leogmendoza/chip8-emulator/platform/stm32/rom_catalog.c

#include "rom_catalog.h"

#ifdef PLATFORM_STM32

#include <stdint.h>

// -- ROM List --
const char *rom_list[] = {
    "tetris",
    "space_invaders",
    "tic_tac_toe",
    "brix",
    "pong",
    "connect_4",
    "puzzle",
    "blinky",
    "test_opcode"
};
const int rom_count = (int)(sizeof(rom_list) / sizeof(rom_list[0]));

// -- ROM configs --
// TODO: Change each ROM's config params when PCB arrives!!!
const RomConfig rom_configs[] = {
    { "tetris",         DEFAULT_INSTRUCTIONS_PER_FRAME, DEFAULT_CPU_CYCLE_DELAY_MS },
    { "space_invaders", DEFAULT_INSTRUCTIONS_PER_FRAME, DEFAULT_CPU_CYCLE_DELAY_MS },
    { "tic_tac_toe",    30, DEFAULT_CPU_CYCLE_DELAY_MS },
    { "brix",           15, DEFAULT_CPU_CYCLE_DELAY_MS },
    { "pong",           15, DEFAULT_CPU_CYCLE_DELAY_MS },
    { "connect_4",      10, DEFAULT_CPU_CYCLE_DELAY_MS },
    { "puzzle",         DEFAULT_INSTRUCTIONS_PER_FRAME, DEFAULT_CPU_CYCLE_DELAY_MS },
    { "blinky",         DEFAULT_INSTRUCTIONS_PER_FRAME, DEFAULT_CPU_CYCLE_DELAY_MS },
    { "test_opcode",    DEFAULT_INSTRUCTIONS_PER_FRAME, DEFAULT_CPU_CYCLE_DELAY_MS },
};
const int rom_config_count = sizeof(rom_configs) / sizeof(rom_configs[0]);

// -- ROM Hex Dumps -- 
const uint8_t rom_tetris[] = {
  0xa2, 0xb4, 0x23, 0xe6, 0x22, 0xb6, 0x70, 0x01, 0xd0, 0x11, 0x30, 0x25,
  0x12, 0x06, 0x71, 0xff, 0xd0, 0x11, 0x60, 0x1a, 0xd0, 0x11, 0x60, 0x25,
  0x31, 0x00, 0x12, 0x0e, 0xc4, 0x70, 0x44, 0x70, 0x12, 0x1c, 0xc3, 0x03,
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
  0x80, 0x80, 0x80, 0x80, 0x80, 0x80, 0x80, 0x80, 0x80, 0x80, 0x80, 0x80,
  0x1a, 0x1a, 0x1a, 0x1a, 0x1a, 0x1a, 0x1a, 0x1a, 0x1a, 0x1a, 0x1a, 0x1a,
  0x1a, 0x1a
};
const int rom_connect_4_len = sizeof(rom_connect_4);

#endif
