leogmendoza/chip8-emulator/platform/pc/display.c

#include "display.h"

#ifdef PLATFORM_PC

#include <SDL2/SDL.h>

#include "chip8.h"

typedef struct {
    SDL_Window   *window;
    SDL_Renderer *renderer;
    SDL_Texture  *texture;
} SdlVideoConfig;

static SdlVideoConfig sdl_video_config = {NULL, NULL, NULL};
static uint32_t pixels[DISPLAY_SIZE];

int platform_display_init(int scale) {
    // Set up SDL video subsystem
    if (SDL_Init(SDL_INIT_VIDEO) < 0) {
        SDL_Log("SDL video subsystem could not be initialized: %s\n", SDL_GetError());

        return 1;
    }

    // Create scaled-up window (currently from 64x32 to 640x320)
    sdl_video_config.window = SDL_CreateWindow(
        "CHIP-8 Emulator by Leopoldo Mendoza",
        SDL_WINDOWPOS_CENTERED, SDL_WINDOWPOS_CENTERED,
        DISPLAY_WIDTH * scale, DISPLAY_HEIGHT * scale,
        SDL_WINDOW_SHOWN
    );

    if (!sdl_video_config.window) {
        SDL_Log("Window could not be created: %s\n", SDL_GetError());

        return 1;
    }

    // Create accelerated renderer
    sdl_video_config.renderer = SDL_CreateRenderer(sdl_video_config.window, -1, SDL_RENDERER_ACCELERATED);

    if (!sdl_video_config.renderer) {
        SDL_Log("Renderer could not be created: %s\n", SDL_GetError());

        return 1;
    }

    // Create texture (64x32 pixel buffer, 32-bit RGBA format)
    sdl_video_config.texture = SDL_CreateTexture(
        sdl_video_config.renderer,
        SDL_PIXELFORMAT_RGBA8888,
        SDL_TEXTUREACCESS_STREAMING,
        DISPLAY_WIDTH,
        DISPLAY_HEIGHT
    );
    if (!sdl_video_config.texture) {
        SDL_Log("Texture could not be created: %s\n", SDL_GetError());
         
        return 1;
    }

    return 0;
}

void platform_display_destroy(void) {
    SDL_DestroyTexture(sdl_video_config.texture);
    SDL_DestroyRenderer(sdl_video_config.renderer);
    SDL_DestroyWindow(sdl_video_config.window);
    SDL_Quit();
}

void platform_display_draw(const uint8_t *framebuffer) {
    // Map CHIP-8 display to 32-bit white or black
    for (int i = 0; i < DISPLAY_SIZE; i++) {
        pixels[i] = ( framebuffer[i] ? 0xFFFFFFFF : 0x000000FF );
    }

    // Copy pixels into texture
    SDL_UpdateTexture(sdl_video_config.texture, NULL, pixels, DISPLAY_WIDTH * sizeof(uint32_t));

    // Clear window
    SDL_RenderClear(sdl_video_config.renderer);

    // Copy texture onto window
    SDL_RenderCopy(sdl_video_config.renderer, sdl_video_config.texture, NULL, NULL);

    // Show new frame
    SDL_RenderPresent(sdl_video_config.renderer);
}

int platform_display_poll_events(void) {
    SDL_Event e;

    while (SDL_PollEvent(&e)) {
        // Exit window
        if (e.type == SDL_QUIT) {
            return 0;
        }
    }

    return 1;
}

#endif
